brotchie/starpusher/starpusher.py

from typing import List, Tuple

import struct
import socket
import math

MAX_PIXELS_PER_UDP_PACKET = 488

GAMMA_CORRECTION = [
    0,
    0,
    0,
    0,
    0,
    0,
    0,
    0,
    0,
    0,
    0,
    0,
    0,
    0,
    0,
    0,
    0,
    0,
    0,
    0,
    0,
    0,
    0,
    0,
    0,
    0,
    0,
    0,
    1,
    1,
    1,
    1,
    1,
    1,
    1,
    1,
    1,
    1,
    1,
    1,
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
]


def gamma_correct(buffer):
    gamma_buffer = []
    for r, g, b in buffer:
        gamma_buffer.append(
            (GAMMA_CORRECTION[r], GAMMA_CORRECTION[g], GAMMA_CORRECTION[b])
        )
    return gamma_buffer


def chunked(lst, max_chunk_size=MAX_PIXELS_PER_UDP_PACKET):
    total_length = len(lst)
    num_chunks = math.ceil(total_length / max_chunk_size)
    avg_chunk_size = math.ceil(total_length / num_chunks)

    start = 0
    for _ in range(num_chunks):
        end = min(start + avg_chunk_size, total_length)
        yield start, lst[start:end]
        start = end


def _send(ip: str, port: int, packet: bytes) -> None:
    sock = socket.socket(socket.AF_INET, socket.SOCK_DGRAM)

    try:
        sock.sendto(packet, (ip, port))
    except socket.error as e:
        print(f"Error sending UDP packet: {e}")
    finally:
        sock.close()


def _build_packet(
    port: int, start_index: int, colors: List[Tuple[int, int, int]]
) -> bytes:
    packet = b"*P"
    packet += struct.pack("<BHH", port, start_index, len(colors))
    for r, g, b in colors:
        packet += struct.pack("<BBB", r, g, b)
    return packet


class Starpusher:
    def __init__(self, ip: str, udp_port: int, gamma_corrected=False):
        self.ip = ip
        self.udp_port = udp_port
        self.gamma_corrected = gamma_corrected

    def send(self, output_port: int, buffer: List[Tuple[int, int, int]]):
        if self.gamma_corrected:
            buffer = gamma_correct(buffer)
        for start, chunk in chunked(buffer):
            _send(self.ip, self.udp_port, _build_packet(output_port, start, chunk))
